Myles24/esp32_mail_detector/mailbox 1.jpg

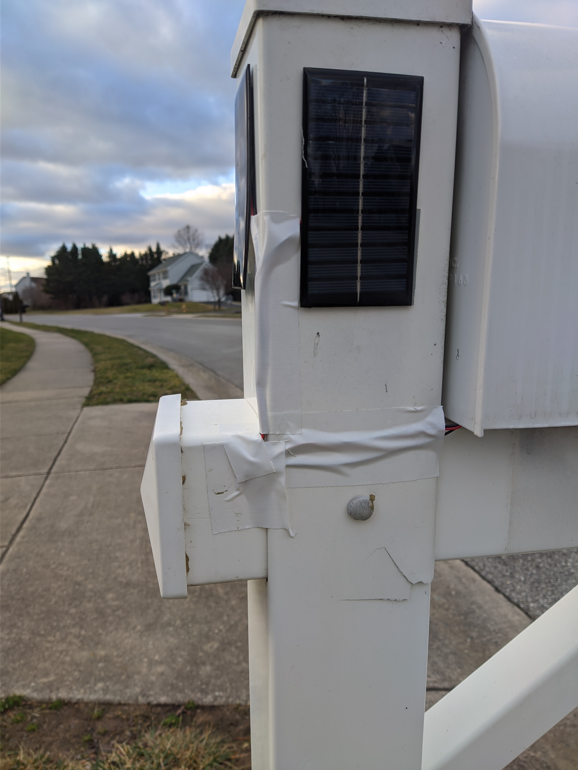
mailbox 1.jpg
